KK153402/Digispark_1KeyBoard/hardware/1Keyboard.kicad_sch

## KiCad design hardware/1Keyboard.kicad_sch (2026-03-05)

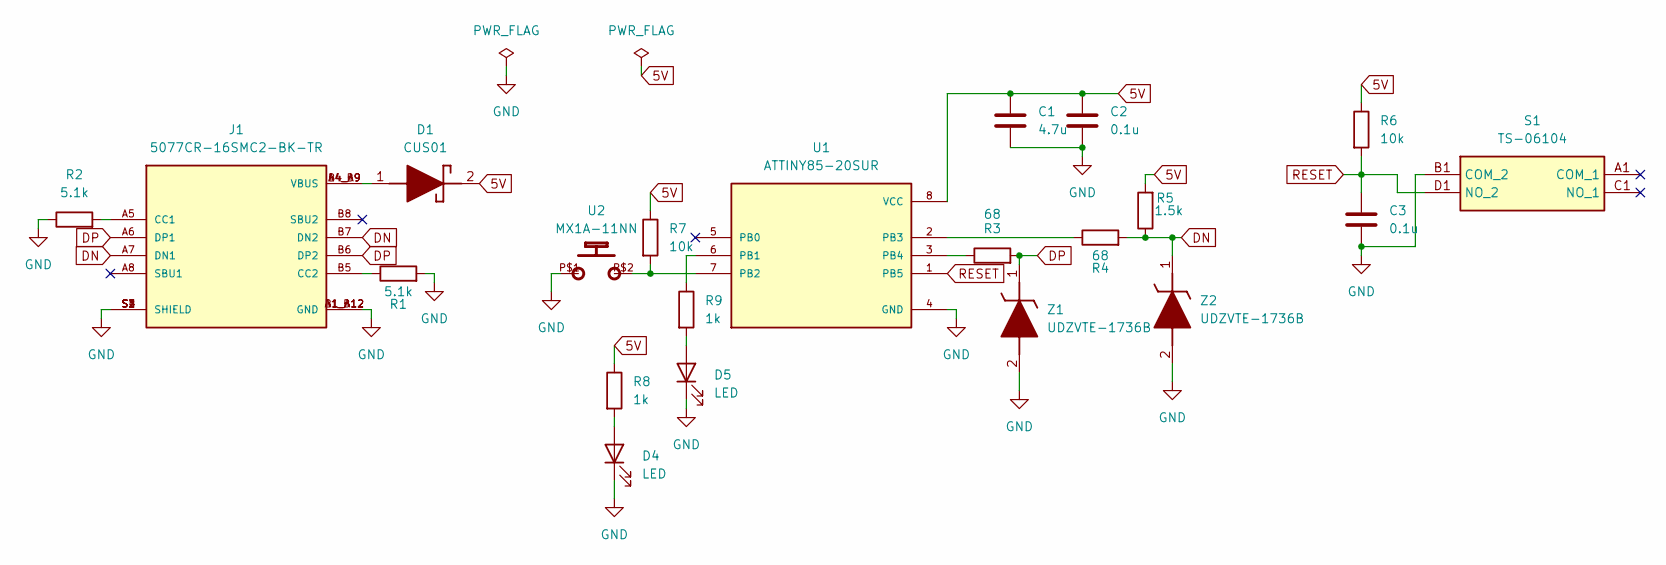
[picture p6: schematic 1Keyboard.kicad_sch]

Parts:
C1: 4.7u; C_0603_1608Metric
C2, C3: 0.1u; C_0603_1608Metric
D1: CUS01; CUS01TE85LQM; Manufacturer_Part_Number CUS01(TE85L,Q,M)
D4, D5: LED; LEDC1608X36N
J1: 5077CR-16SMC2-BK-TR; NELTRON_5077CR-16SMC2-BK-TR
R1, R2: 5.1k; R_0603_1608Metric
R3, R4: 68; R_0603_1608Metric
R5: 1.5k; R_0603_1608Metric
R6, R7: 10k; R_0603_1608Metric
R8, R9: 1k; R_0603_1608Metric
S1: TS-06104; TS06104; Manufacturer_Part_Number TS-06104
U1: ATTINY85-20SUR; SOIC127P798X216-8N
U2: MX1A-11NN; CHERRY_MX1A-11NN_SWITCH
Z1, Z2: UDZVTE-1736B; UDZVTE1736B; Manufacturer_Part_Number UDZVTE-1736B; Mouser Part Number 755-UDZVTE-1736B

Connections:
5V: C1.1, C2.1, D1.2 (K), R5.2, R6.1, R7.1, R8.1, U1.8 (VCC)
DN: J1.A7 (DN1), J1.B7 (DN2), R4.2, R5.1, Z2.1 (K)
DP: J1.A6 (DP1), J1.B6 (DP2), R3.2, Z1.1 (K)
GND: C1.2, C2.2, C3.2, D4.1 (K), D5.1 (K), J1.A1_B12 (GND), J1.B1_A12 (GND), J1.S1 (SHIELD), J1.S2 (SHIELD), J1.S3 (SHIELD), J1.S4 (SHIELD), R1.2, R2.1, S1.B1 (COM_2), U1.4 (GND), U2.P$1, Z1.2 (A), Z2.2 (A)
unnamed: D1.1 (A), J1.A4_B9 (VBUS), J1.B4_A9 (VBUS)
unnamed: D4.2 (A), R8.2
unnamed: D5.2 (A), R9.2
unnamed: J1.A5 (CC1), R2.2
unnamed: J1.B5 (CC2), R1.1
unnamed: R3.1, U1.3 (PB4)
unnamed: R4.1, U1.2 (PB3)
unnamed: R7.2, U1.7 (PB2), U2.P$2
unnamed: R9.1, U1.6 (PB1)
RESET: C3.1, R6.2, S1.D1 (NO_2), U1.1 (PB5)
